stardustArc/lemonshark_/photos/DSC_6443.JPG

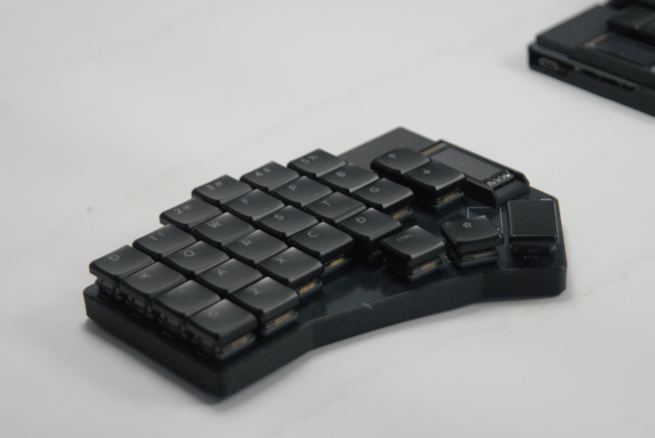
photos/DSC_6443.JPG
