stardustArc/lemonshark_/photos/DSC_6445.JPG

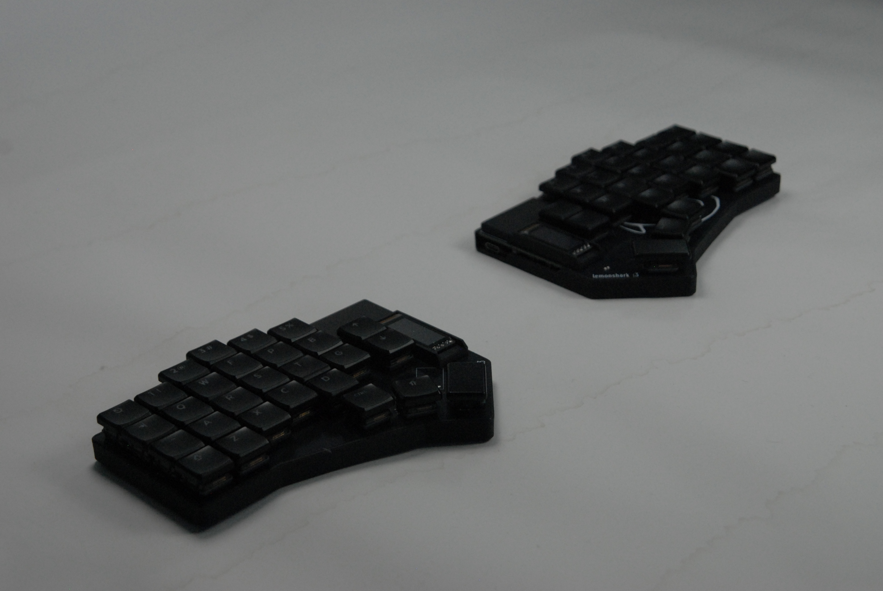
photos/DSC_6445.JPG
