stardustArc/lemonshark_/photos/DSC_6524.JPG

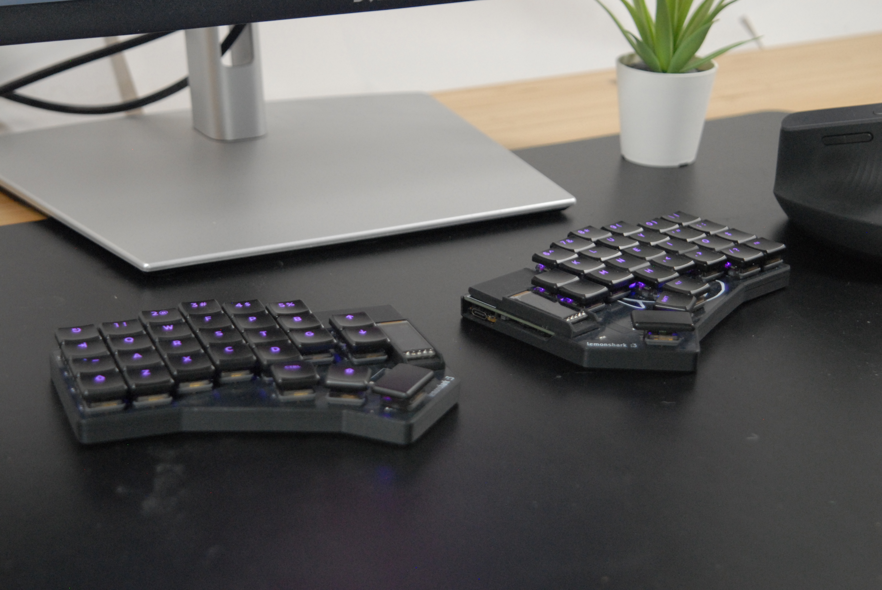
photos/DSC_6524.JPG
