stardustArc/lemonshark_/photos/DSC_6586.JPG

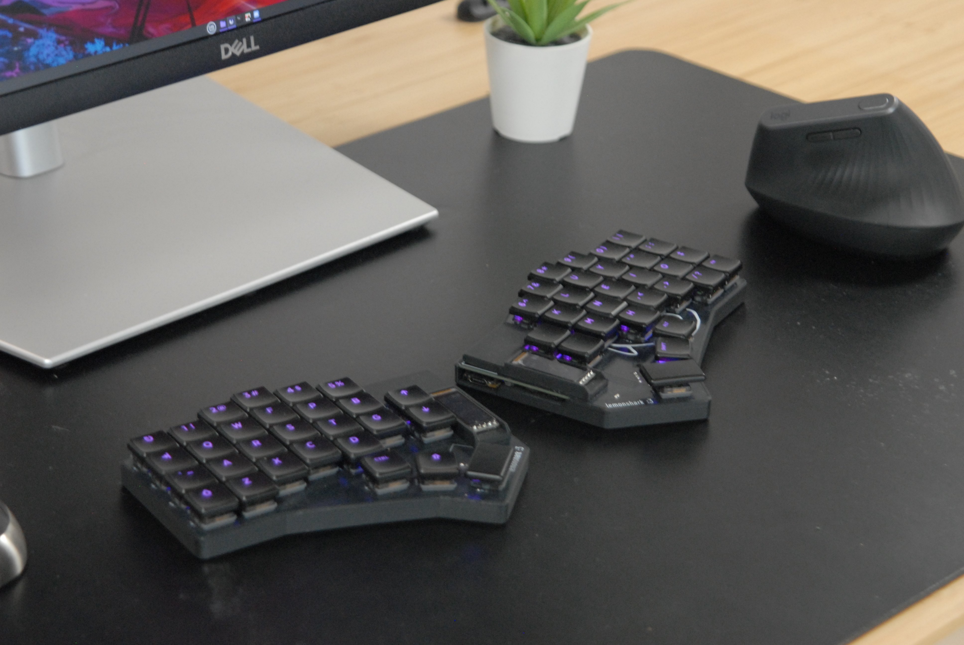
photos/DSC_6586.JPG
